SasaKaranovic/RingClock/Firmware/Application/main.h

#ifndef __MAIN_H__
#define __MAIN_H__

#include <stm32f1xx.h>
#include <stm32f1xx_hal_gpio.h>
#include <stdint.h>
#include <stdlib.h>
#include <stdio.h>
#include <string.h>
#include "sys_init.h"
#include "ws2812b.h"
#include "clock.h"
#include "debug.h"
#include "uart.h"


#define _UNUSED(x) ( (void) x )


#endif
